Ttl/fmcw2/host/libhackrf/src/hackrf.h

/*
Copyright (c) 2012, Jared Boone <jared@sharebrained.com>
Copyright (c) 2013, Benjamin Vernoux <titanmkd@gmail.com>
Copyright (c) 2013, Michael Ossmann <mike@ossmann.com>

All rights reserved.

Redistribution and use in source and binary forms, with or without modification, are permitted provided that the following conditions are met:

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
THIS SOFTWARE IS PROVIDED BY THE COPYRIGHT HOLDERS AND CONTRIBUTORS "AS IS" AND ANY EXPRESS OR IMPLIED WARRANTIES, INCLUDING, BUT NOT LIMITED TO, 
THE IMPLIED WARRANTIES OF MERCHANTABILITY AND FITNESS FOR A PARTICULAR PURPOSE ARE DISCLAIMED.
IN NO EVENT SHALL THE COPYRIGHT HOLDER OR CONTRIBUTORS BE LIABLE FOR ANY DIRECT, INDIRECT, INCIDENTAL, SPECIAL, EXEMPLARY, OR CONSEQUENTIAL DAMAGES
(INCLUDING, BUT NOT LIMITED TO, PROCUREMENT OF SUBSTITUTE GOODS OR SERVICES; LOSS OF USE, DATA, OR PROFITS; OR BUSINESS INTERRUPTION)
HOWEVER CAUSED AND ON ANY THEORY OF LIABILITY, WHETHER IN CONTRACT, STRICT LIABILITY, OR TORT (INCLUDING NEGLIGENCE OR OTHERWISE)
ARISING IN ANY WAY OUT OF THE USE OF THIS SOFTWARE, EVEN IF ADVISED OF THE POSSIBILITY OF SUCH DAMAGE.
*/

#ifndef __HACKRF_H__
#define __HACKRF_H__

#include <stdint.h>

#ifdef _WIN32
   #define ADD_EXPORTS
   
  /* You should define ADD_EXPORTS *only* when building the DLL. */
  #ifdef ADD_EXPORTS
    #define ADDAPI __declspec(dllexport)
  #else
    #define ADDAPI __declspec(dllimport)
  #endif

  /* Define calling convention in one place, for convenience. */
  #define ADDCALL __cdecl

#else /* _WIN32 not defined. */

  /* Define with no value on non-Windows OSes. */
  #define ADDAPI
  #define ADDCALL

#endif

enum hackrf_error {
	HACKRF_SUCCESS = 0,
	HACKRF_TRUE = 1,
	HACKRF_ERROR_INVALID_PARAM = -2,
	HACKRF_ERROR_NOT_FOUND = -5,
	HACKRF_ERROR_BUSY = -6,
	HACKRF_ERROR_NO_MEM = -11,
	HACKRF_ERROR_LIBUSB = -1000,
	HACKRF_ERROR_THREAD = -1001,
	HACKRF_ERROR_STREAMING_THREAD_ERR = -1002,
	HACKRF_ERROR_STREAMING_STOPPED = -1003,
	HACKRF_ERROR_STREAMING_EXIT_CALLED = -1004,
	HACKRF_ERROR_OTHER = -9999,
};

enum hackrf_board_id {
	BOARD_ID_JELLYBEAN  = 0,
	BOARD_ID_JAWBREAKER = 1,
	BOARD_ID_HACKRF_ONE = 2,
	BOARD_ID_INVALID = 0xFF,
};

enum hackrf_usb_board_id {
	USB_BOARD_ID_JAWBREAKER = 0x604B,
	USB_BOARD_ID_HACKRF_ONE = 0x6099,
	USB_BOARD_ID_RAD1O = 0xCC15,
	USB_BOARD_ID_INVALID = 0xFFFF,
};

enum rf_path_filter {
	RF_PATH_FILTER_BYPASS = 0,
	RF_PATH_FILTER_LOW_PASS = 1,
	RF_PATH_FILTER_HIGH_PASS = 2,
};

typedef enum {
	TRANSCEIVER_MODE_OFF = 0,
	TRANSCEIVER_MODE_RX = 1,
	TRANSCEIVER_MODE_TX = 2,
	TRANSCEIVER_MODE_SS = 3,
	TRANSCEIVER_MODE_CPLD_UPDATE = 4
} transceiver_mode_t;

typedef struct hackrf_device hackrf_device;

typedef struct {
	hackrf_device* device;
	uint8_t* buffer;
	int buffer_length;
	int valid_length;
	void* rx_ctx;
	void* tx_ctx;
} hackrf_transfer;

typedef struct {
	uint32_t part_id[2];
	uint32_t serial_no[4];
} read_partid_serialno_t;


struct hackrf_device_list {
	char **serial_numbers;
	enum hackrf_usb_board_id *usb_board_ids;
	int *usb_device_index;
	int devicecount;
	
	void **usb_devices;
	int usb_devicecount;
};
typedef struct hackrf_device_list hackrf_device_list_t;

typedef int (*hackrf_sample_block_cb_fn)(hackrf_transfer* transfer);

#ifdef __cplusplus
extern "C"
{
#endif

extern ADDAPI int ADDCALL hackrf_init();
extern ADDAPI int ADDCALL hackrf_exit();

extern ADDAPI hackrf_device_list_t* ADDCALL hackrf_device_list();
extern ADDAPI int ADDCALL hackrf_device_list_open(hackrf_device_list_t *list, int idx, hackrf_device** device);
extern ADDAPI void ADDCALL hackrf_device_list_free(hackrf_device_list_t *list);
 
extern ADDAPI int ADDCALL hackrf_open(hackrf_device** device);
extern ADDAPI int ADDCALL hackrf_open_by_serial(const char* const desired_serial_number, hackrf_device** device);
extern ADDAPI int ADDCALL hackrf_close(hackrf_device* device);
 
extern ADDAPI int ADDCALL hackrf_start_rx(hackrf_device* device, hackrf_sample_block_cb_fn callback, void* rx_ctx);
extern ADDAPI int ADDCALL hackrf_stop_rx(hackrf_device* device);
 
/* return HACKRF_TRUE if success */
extern ADDAPI int ADDCALL hackrf_is_streaming(hackrf_device* device);
 
extern ADDAPI int ADDCALL hackrf_spiflash_erase(hackrf_device* device);
extern ADDAPI int ADDCALL hackrf_spiflash_write(hackrf_device* device, const uint32_t address, const uint16_t length, unsigned char* const data);
extern ADDAPI int ADDCALL hackrf_spiflash_read(hackrf_device* device, const uint32_t address, const uint16_t length, unsigned char* data);

extern ADDAPI int ADDCALL hackrf_board_id_read(hackrf_device* device, uint8_t* value);
extern ADDAPI int ADDCALL hackrf_version_string_read(hackrf_device* device, char* version, uint8_t length);

extern ADDAPI int ADDCALL hackrf_board_partid_serialno_read(hackrf_device* device, read_partid_serialno_t* read_partid_serialno);

extern ADDAPI const char* ADDCALL hackrf_error_name(enum hackrf_error errcode);
extern ADDAPI const char* ADDCALL hackrf_board_id_name(enum hackrf_board_id board_id);
extern ADDAPI const char* ADDCALL hackrf_usb_board_id_name(enum hackrf_usb_board_id usb_board_id);
extern ADDAPI const char* ADDCALL hackrf_filter_path_name(const enum rf_path_filter path);

extern ADDAPI int ADDCALL hackrf_set_sweep(hackrf_device* device, double fstart, double bw, double length, int delay);
extern ADDAPI int ADDCALL hackrf_set_adf4158_reg(char *name, unsigned int value);
extern ADDAPI int ADDCALL hackrf_adf4158_to_device(hackrf_device* device);
extern ADDAPI int ADDCALL hackrf_set_mcp(hackrf_device* device, uint32_t value);
extern ADDAPI int ADDCALL hackrf_set_gpio(hackrf_device *device, uint32_t bits);
extern ADDAPI int ADDCALL hackrf_clear_gpio(hackrf_device *device, uint32_t bits);
extern ADDAPI int ADDCALL hackrf_set_clock_divider(hackrf_device *device, uint16_t divider);

#ifdef __cplusplus
} // __cplusplus defined.
#endif

#endif//__HACKRF_H__
